tszaboo/Ortho4Exent/Images/DSC_3321.jpeg

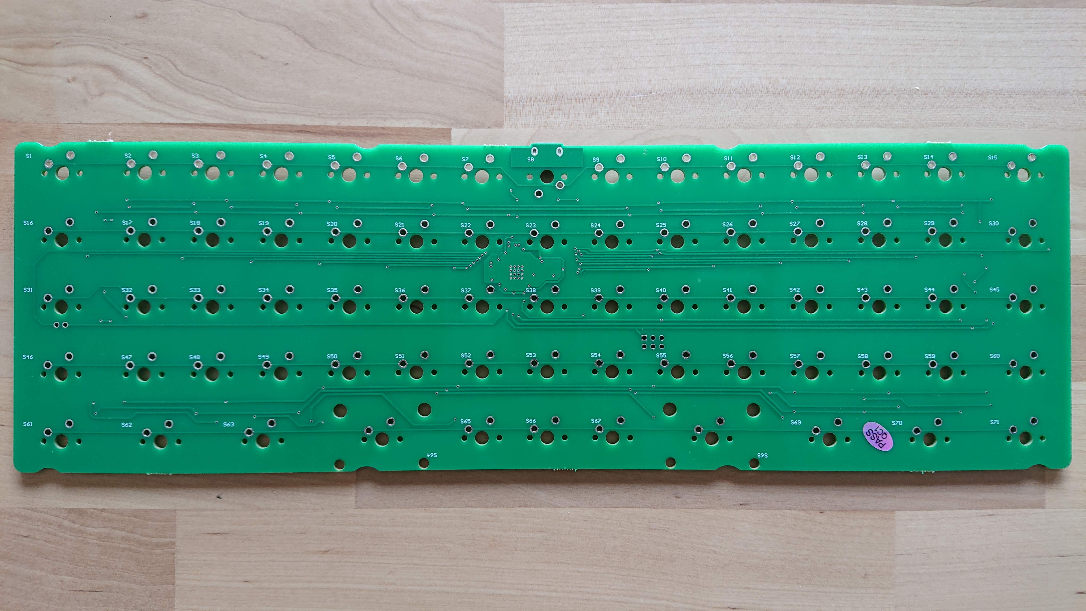
Images/DSC_3321.jpeg
